michalnand/line_sensor/doc/diagrams/top.jpg

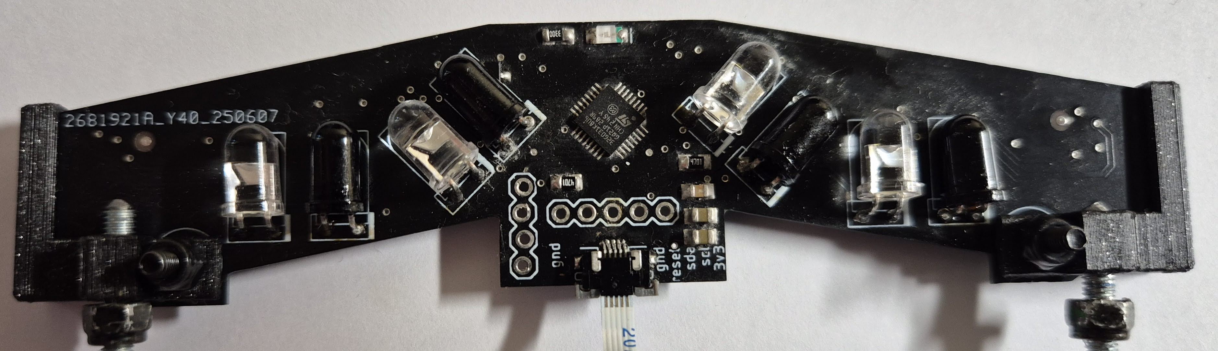
doc/diagrams/top.jpg
