michalnand/line_sensor/doc/images/board_slim_b.png

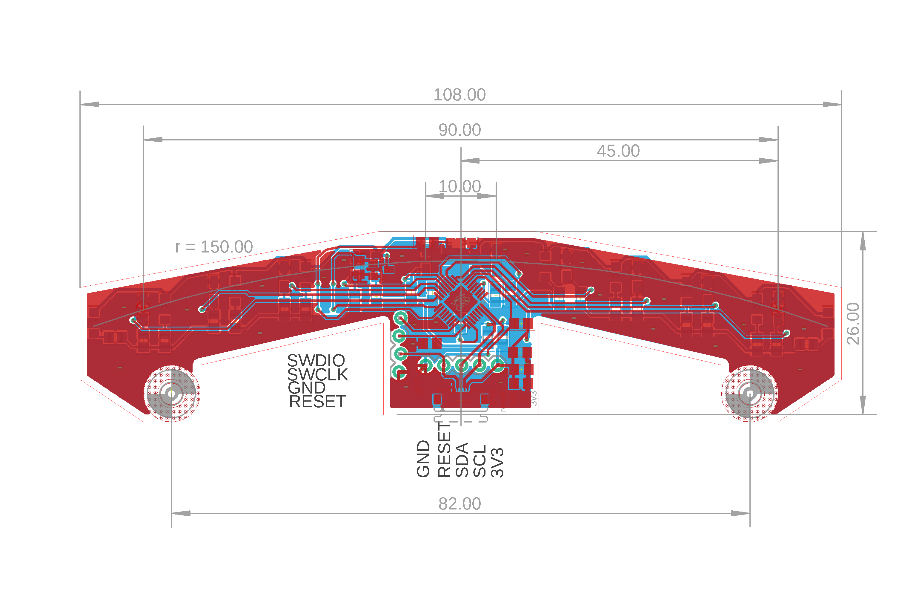
doc/images/board_slim_b.png
