michalnand/line_sensor/doc/images/bottom.png

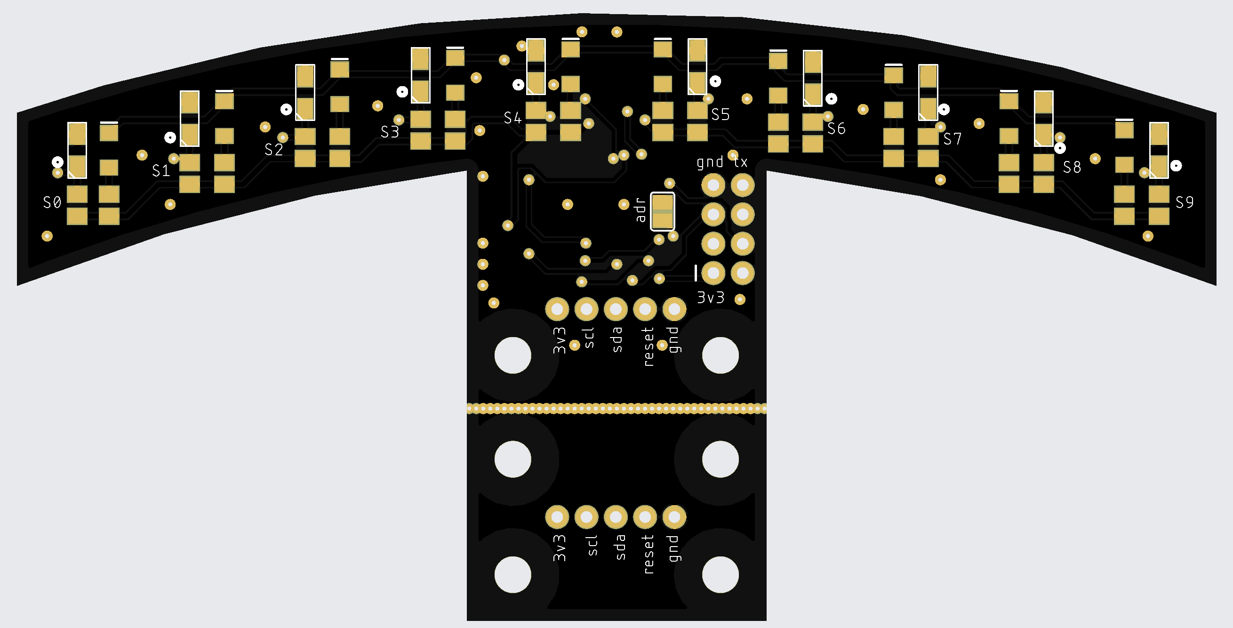
doc/images/bottom.png
