michalnand/line_sensor/doc/images/bottom_3d.png

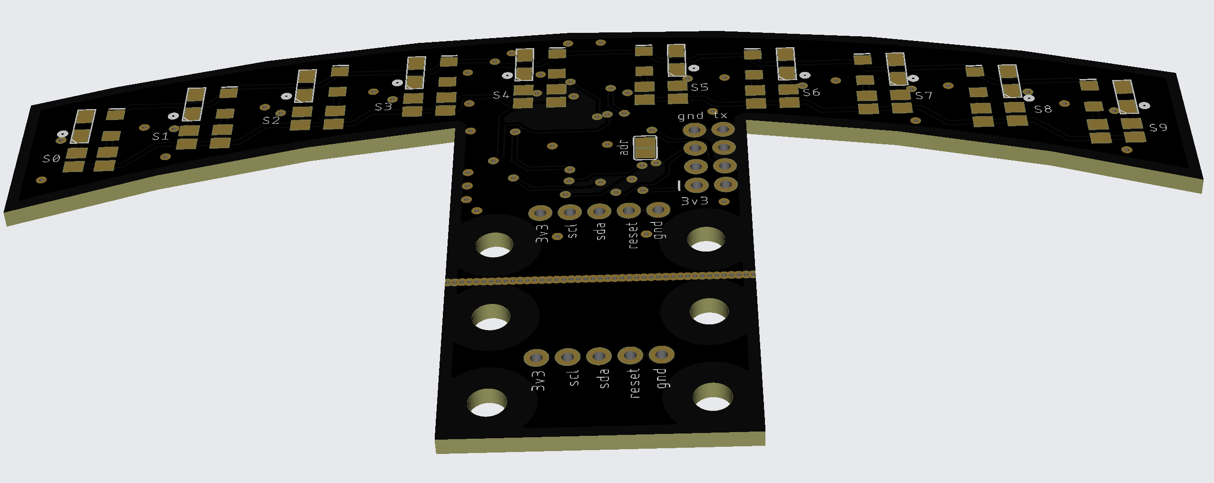
doc/images/bottom_3d.png
