michalnand/line_sensor/doc/images/connectors.png

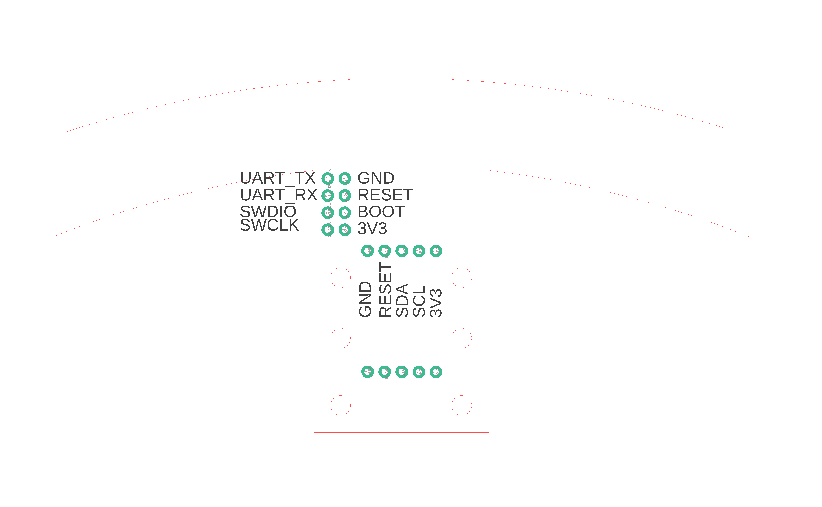
doc/images/connectors.png
