michalnand/line_sensor/doc/images/connectors_b.png

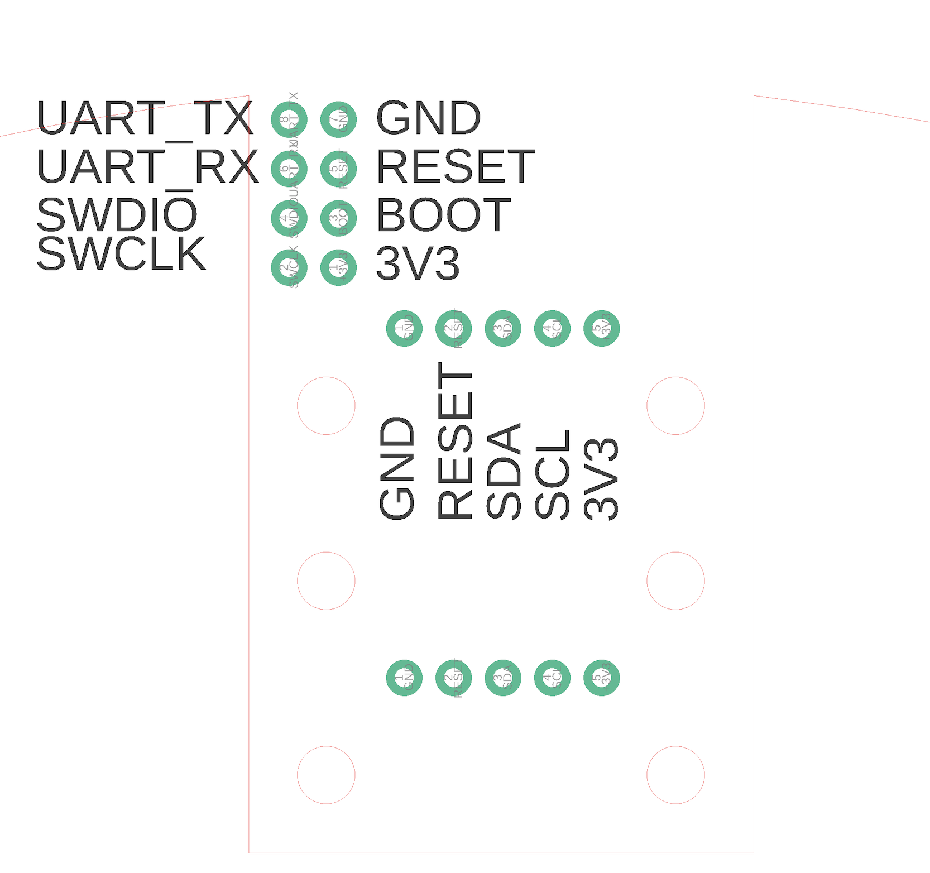
doc/images/connectors_b.png
