michalnand/line_sensor/doc/images/dims_wh.png

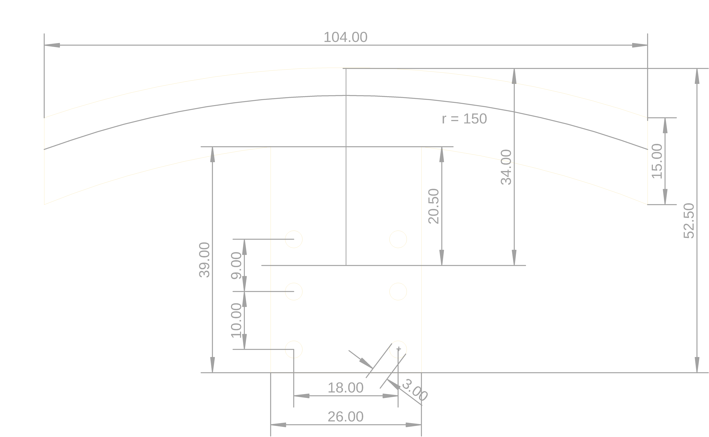
doc/images/dims_wh.png
