michalnand/line_sensor/doc/images/out.png

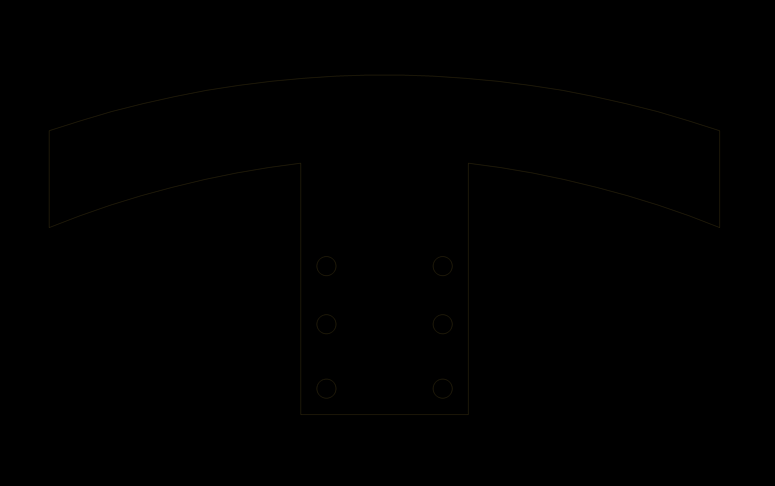
doc/images/out.png
