michalnand/line_sensor/doc/images/out_bin.png

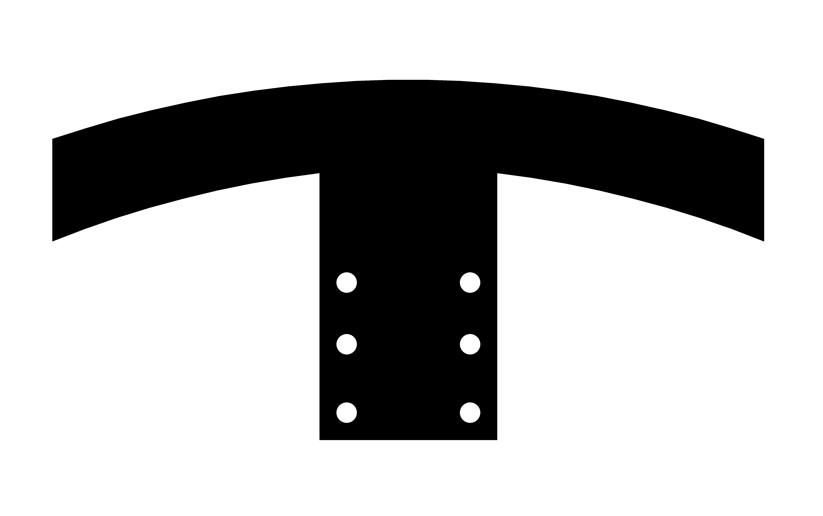
doc/images/out_bin.png
