michalnand/line_sensor/doc/images/schem_slim.png

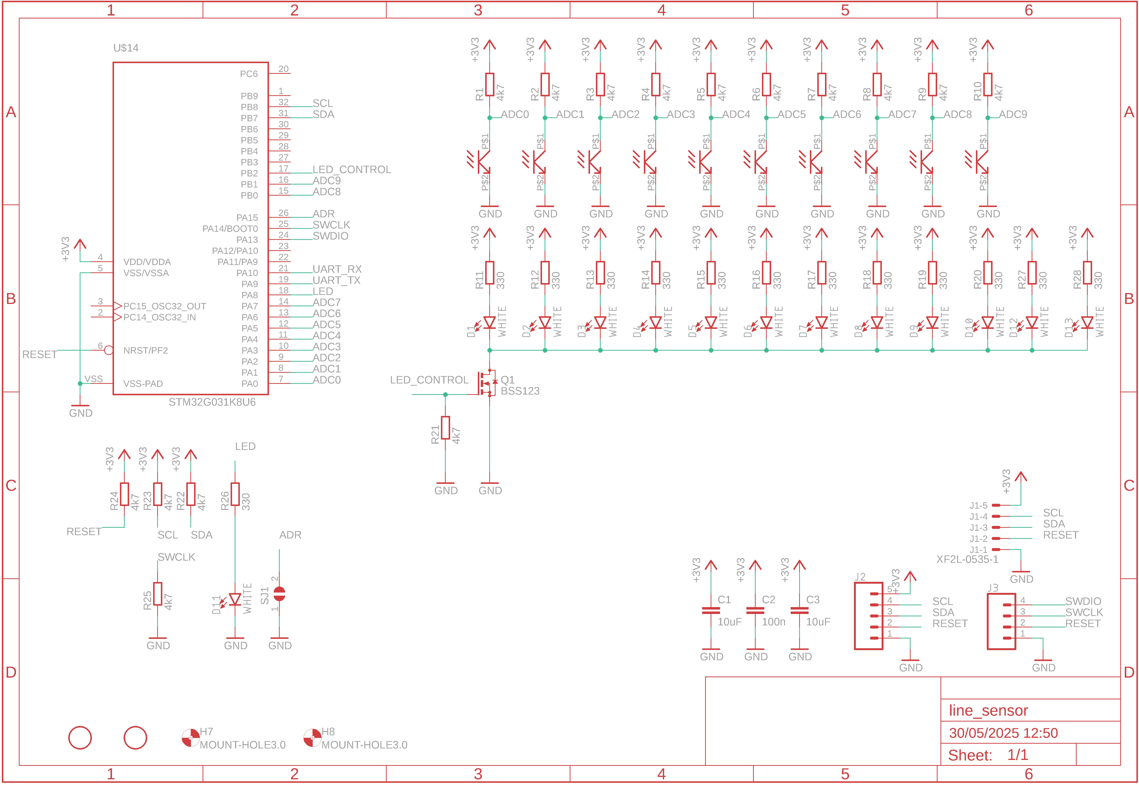
doc/images/schem_slim.png
