michalnand/line_sensor/doc/images/top.png

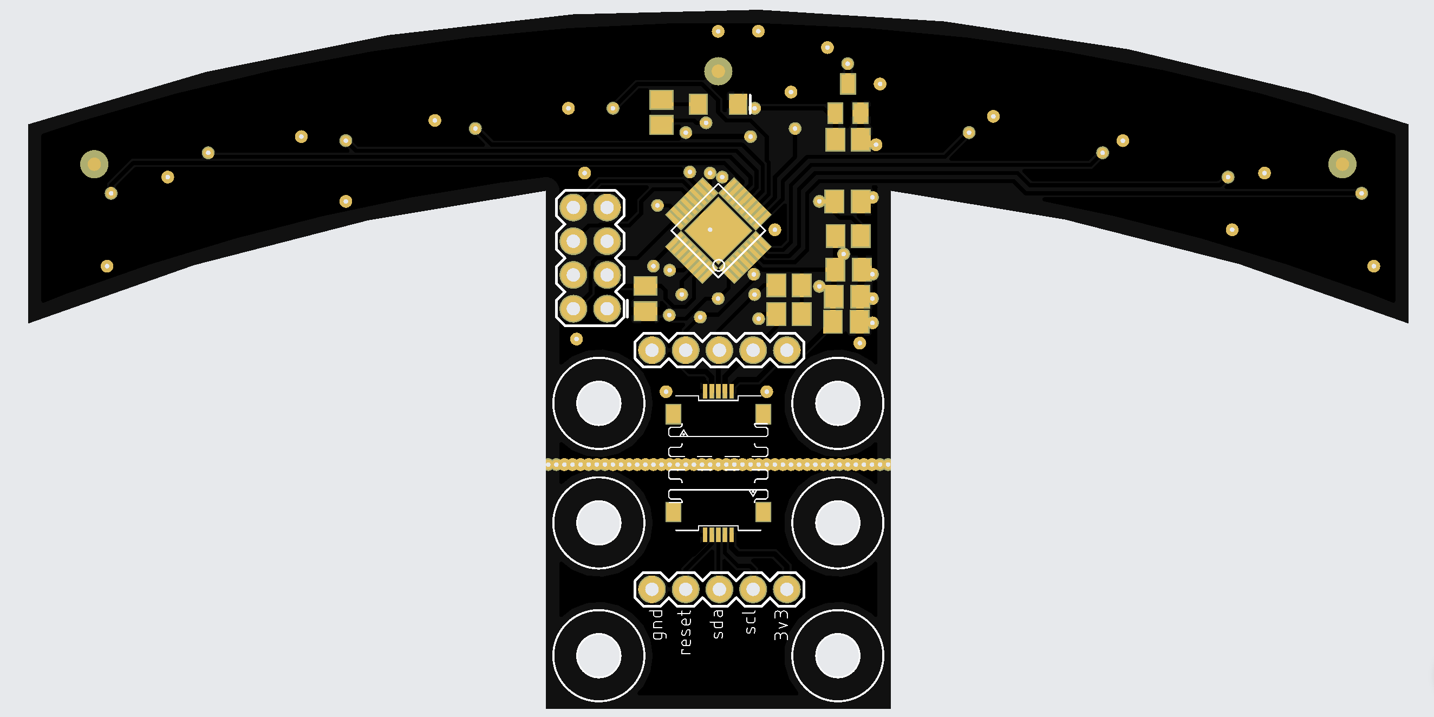
doc/images/top.png
