michalnand/line_sensor/doc/images/3d_parts_1.png

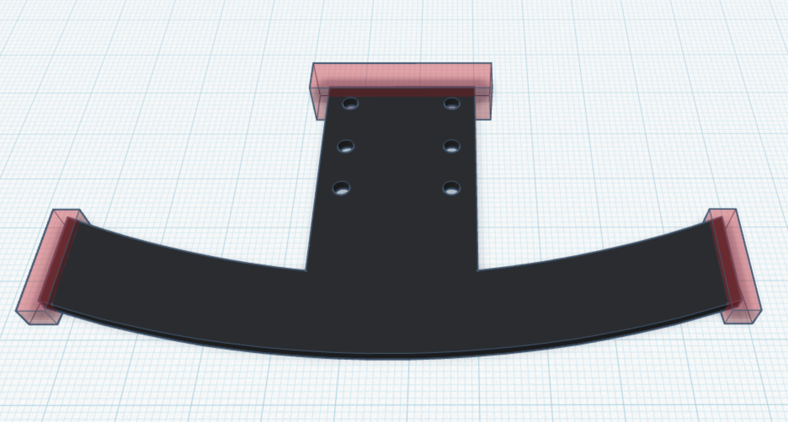
doc/images/3d_parts_1.png
