michalnand/line_sensor/doc/images/3d_parts_2.png

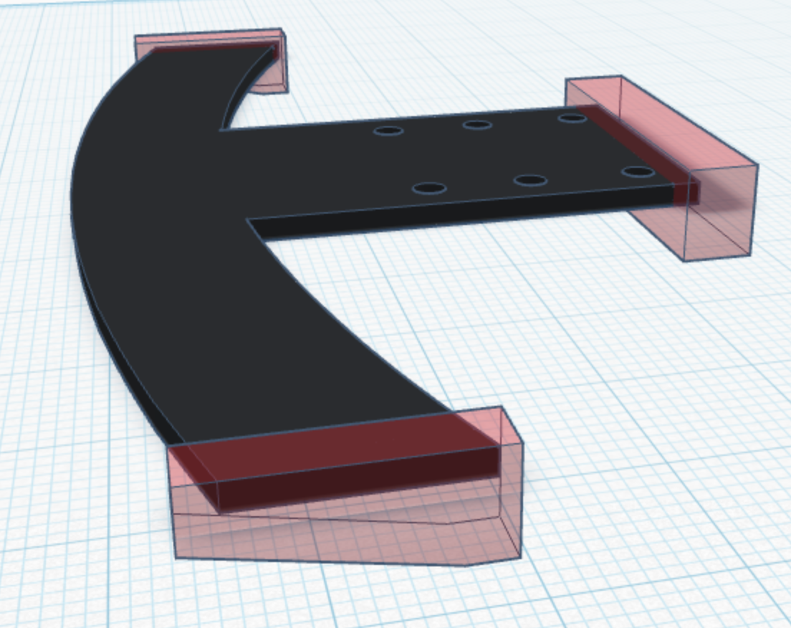
doc/images/3d_parts_2.png
