michalnand/line_sensor/firmware_v3/usr/i2c_slave.h

#ifndef _I2CSlave_H_
#define _I2CSlave_H_

#include "drivers.h"


#define I2C_SLAVE_ADDRESS   ((uint8_t)0x42)
#define I2C_BUFFER_SIZE     ((uint32_t)256)


class I2CSlave
{
    public:
        void init();
        uint8_t is_write_flag();

    private:
        void _i2c_init();

    public:
        uint8_t wr_flag, ptr, state;

    public:
        uint8_t buffer[I2C_BUFFER_SIZE];
};


#endif
